magico13/TrailerController/src/phase0/include/wifi_creds.h

#ifndef WIFI_CREDS_H
#define WIFI_CREDS_H

// Set your wifi credentials here if you want the ESP32 to
// connect to an existing network instead of creating its own
const char* WIFI_SSID = "";
const char* WIFI_PASSWORD = "";

#endif // WIFI_CREDS_H
